ccadic/NewMorphS3-v1/20221112_204421.jpg

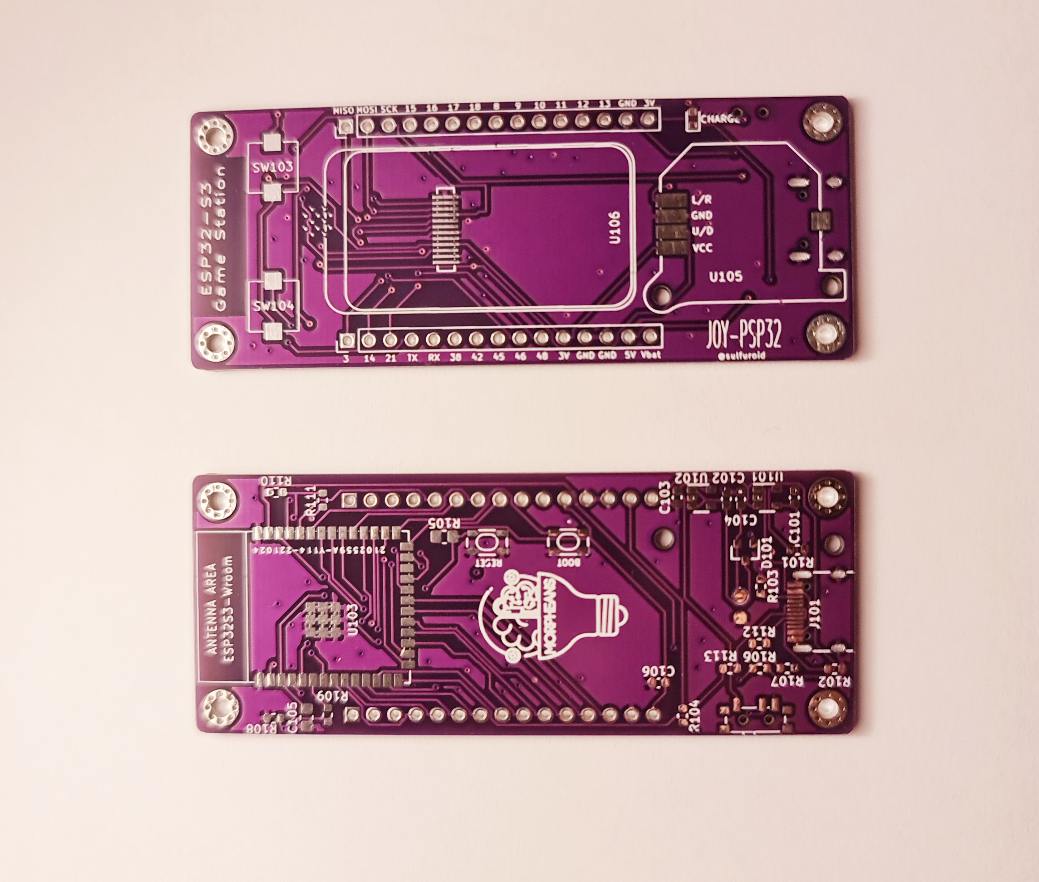
20221112_204421.jpg
