ccadic/NewMorphS3-v1/20221112_204432.jpg

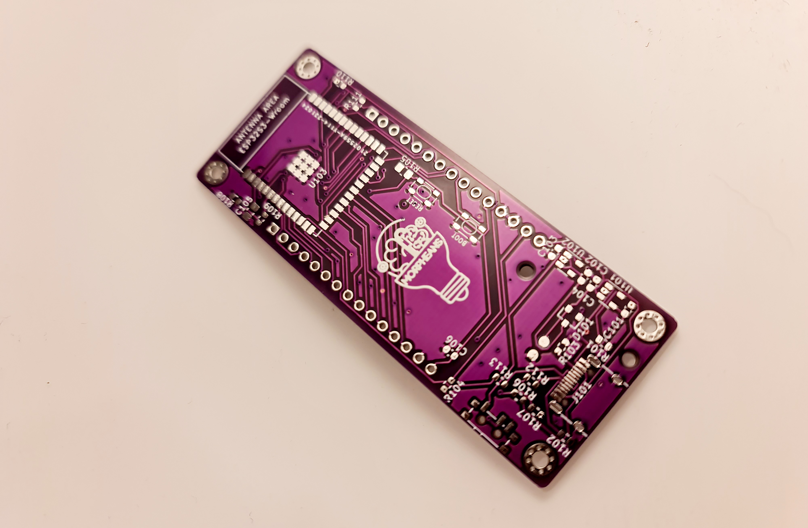
20221112_204432.jpg
