ccadic/NewMorphS3-v1/20221112_204435.jpg

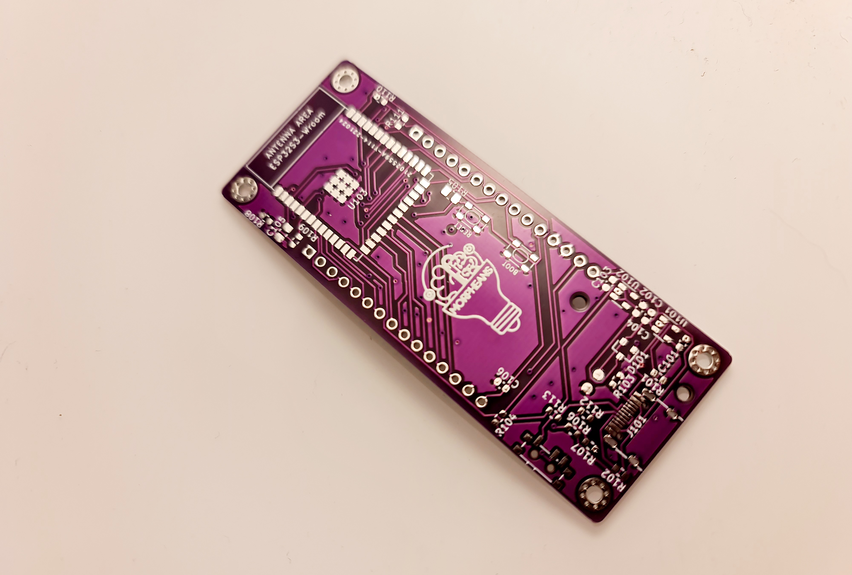
20221112_204435.jpg
