ccadic/NewMorphS3-v1/20221112_204506.jpg

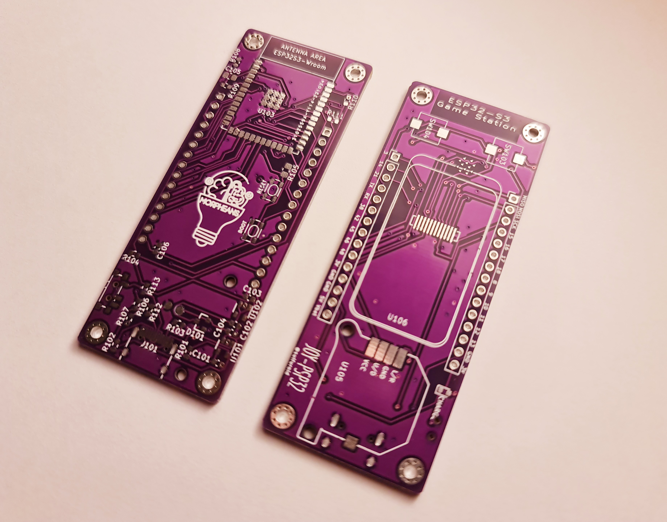
20221112_204506.jpg
