ccadic/NewMorphS3-v1/20221112_204518.jpg

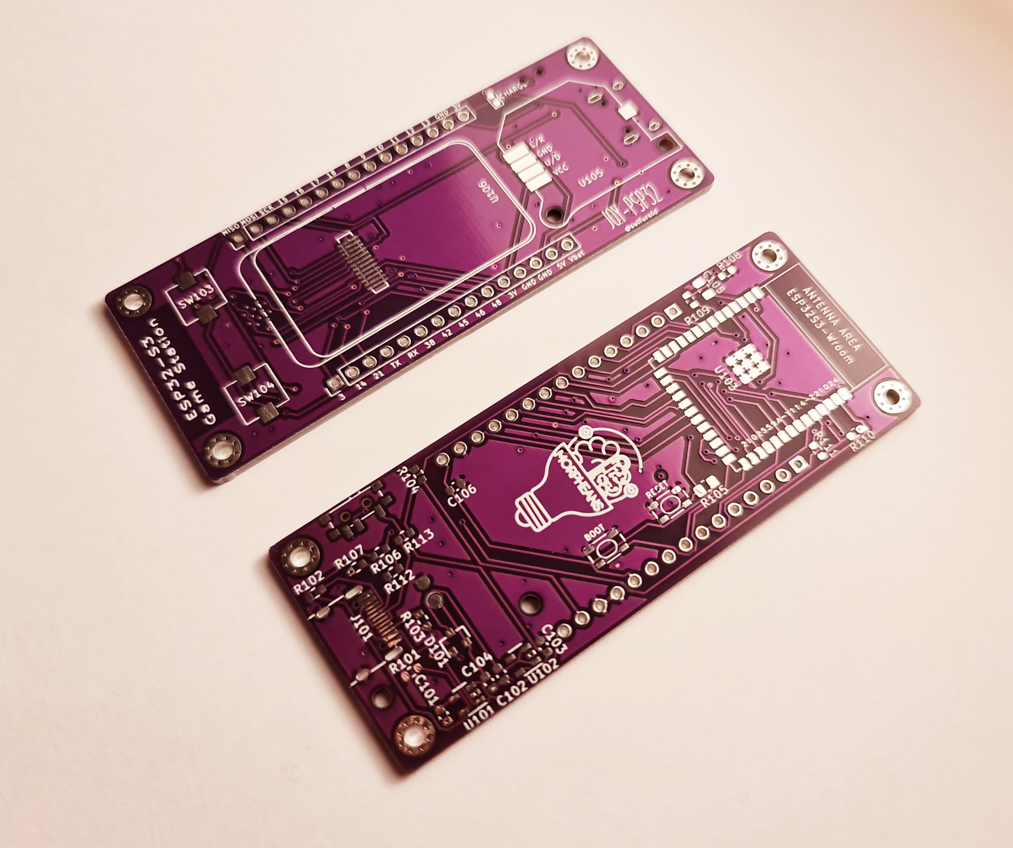
20221112_204518.jpg
