ccadic/NewMorphS3-v1/N0ewmorphS3beta3.jpg

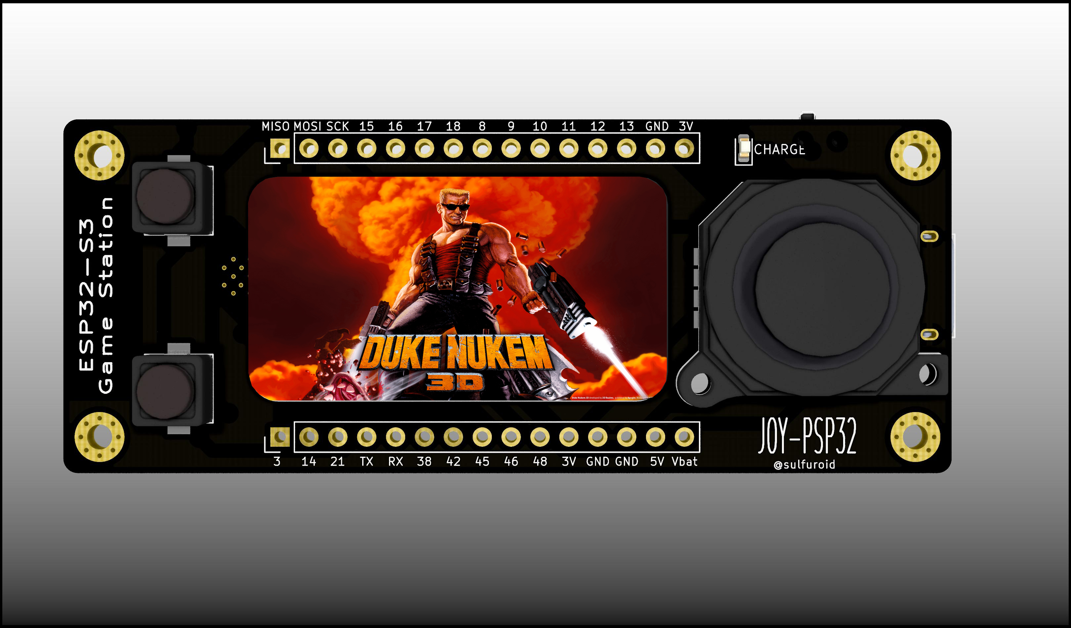
N0ewmorphS3beta3.jpg
