ccadic/NewMorphS3-v1/esp3joystick_samplecode/esp3joystick_samplecode.ino

#include <Adafruit_GFX.h>    // Core graphics library
//#include <Adafruit_ST7735.h> // Hardware-specific library for ST7735
//#include <Adafruit_ST7789.h> // Hardware-specific library for ST7789
#include <SPI.h>


#include <Arduino_ST7789.h> // Hardware-specific library for ST7789 (with or without CS pin)

#define TFT_DC    40
#define TFT_RST   41 
#define TFT_CS    39 // only for displays with CS pin
#define TFT_MOSI  35   // for hardware SPI data pin (all of available pins)
#define TFT_SCLK  36   // for hard        ware SPI sclk pin (all of available pins)
#define TFT_LEDA  5   // for hard        ware SPI sclk pin (all of available pins)


Arduino_ST7789 tft = Arduino_ST7789(TFT_DC, TFT_RST, TFT_MOSI, TFT_SCLK, TFT_CS); //for display with CS pin

#define JoyX 1   // pins are Joystick is connected
#define JoyY 2


// variable for storing the potentiometer value
int jx = 0;
int jy = 0;


// image
const uint16_t mercy [] PROGMEM = {0x2944, 0x20c2, 0x20c2, 0x18c2, 0x18c2, 0x20c2, 0x20c3, 0x20c3, 0x18c3, 0x18c2, 0x18c2, 0x1082, 0x1082, 0x1082, 0x1082, 0x1882, 0x28c3, 0x38c3, 0x4904, 0x5104, 0x5904, 0x5903, 0x5903, 0x5904, 0x5903, 0x5903, 0x5903, 0x5903, 0x5903, 0x6103, 0x6103, 0x6103, 0x6103, 0x6103, 0x6103, 0x6903, 0x6903, 0x6903, 0x6903, 0x7103, 0x7103, 0x7103, 0x70c3, 0x7903, 0x78c3, 0x80c3, 0x88c3, 0x88c3, 0x8903, 0x90c3, 0xb183, 0xe342, 0xf402, 0xfc82, 0xfcc2, 0xfd02, 0xfcc2, 0xfcc2, 0xfc42, 0xfc02, 0xfc42, 0xfc82, 0xfcc2, 0xfd02, 0xfd02, 0xfd02, 0xfcc2, 0xfcc2, 0xfcc2, 0xfc82, 0xfc82, 0xfc02, 0xfbc2, 0xfbc2, 0xfbc2, 0xfb82, 0xfb82, 0xfb82, 0xfb82, 0xfb82, 0xfb42, 0xfb82, 0xfb82, 0xfb42, 0xfb42, 0xfb82, 0xfb82, 0xfb82, 0xfb02, 0xfac2, 0xf282, 0xea82, 0xea82, 0xf2c2, 0xf2c2, 0xe242, 0xda02, 0xd9c2, 0xd982, 0xd142, 0xd182, 0xd982, 0xe242, 0xea82, 0xe242, 0xda02, 0xd982, 0xd982, 0xd142, 0xd942, 0xd142, 0xd142, 0xd142, 0xd142, 0xd9c2, 0xeac2, 0xfb42, 0xf342, 0xfb42, 0xfbc2, 0xfc42, 0xfc02, 0xfb82, 0xfb42, 0xf342, 0xfb42, 0xfc02, 0xfc82, 0xfcc2, 0xfcc2, 0xfc82, 0xfc42, 0xfc02, 0xfc02, 0xfbc2, 0xfbc2, 0xfbc2, 0xfc02, 0xfc42, 0xfc82, 0xfc82, 0xfc42, 0xfbc2, 0xf2c2, 0xd9c2, 0xd142, 0xd142, 0xd982, 0xd9c2, 0xda02, 0xda02, 0xda02, 0xe242, 0xf302, 0xfb42, 0xfb82, 0xfb82, 0xfb42, 0xfb42, 0xf302, 0xf2c2, 0xf302, 0xfb42, 0xfbc2, 0xfc02, 0xfc42, 0xfc82, 0xfc82, 0xfc02, 0xfbc2, 0xfb42, 0xf282, 0xea42, 0xe202, 0xd9c2, 0xd182, 0xd182, 0xd9c2, 0xea82, 0xfb42, 0xfb82, 0xfb42, 0xfb42, 0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
  pinMode(TFT_LEDA, OUTPUT); 
  digitalWrite(TFT_LEDA, HIGH);
  delay (100);

   // DISPLAY WELCOME SCREEN
  tft.init(320, 170);   // initialize a ST7789 chip, 240x240 pixels
  tft.fillScreen(BLACK);
  tft.setRotation(1);
  tft.drawRGBBitmap(0, 0, mercy, 320, 170);
  

  //Serial.println(time, DEC);
  delay(500);
}


void loop() {


}
